Sadrita404/Low-Key/IMAGES/21.png

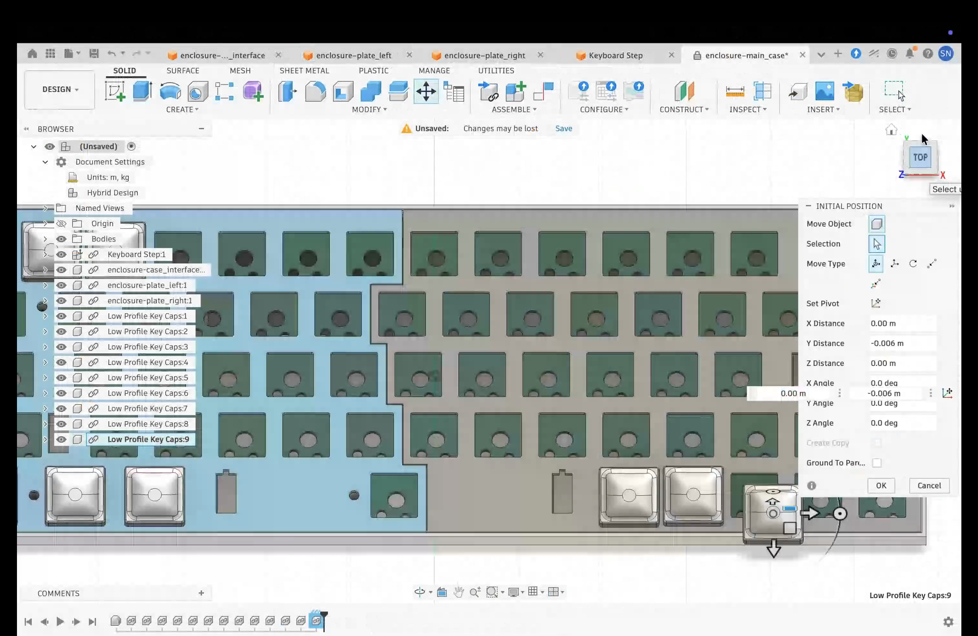
IMAGES/21.png
