Sadrita404/Low-Key/BILL/bill 1.png

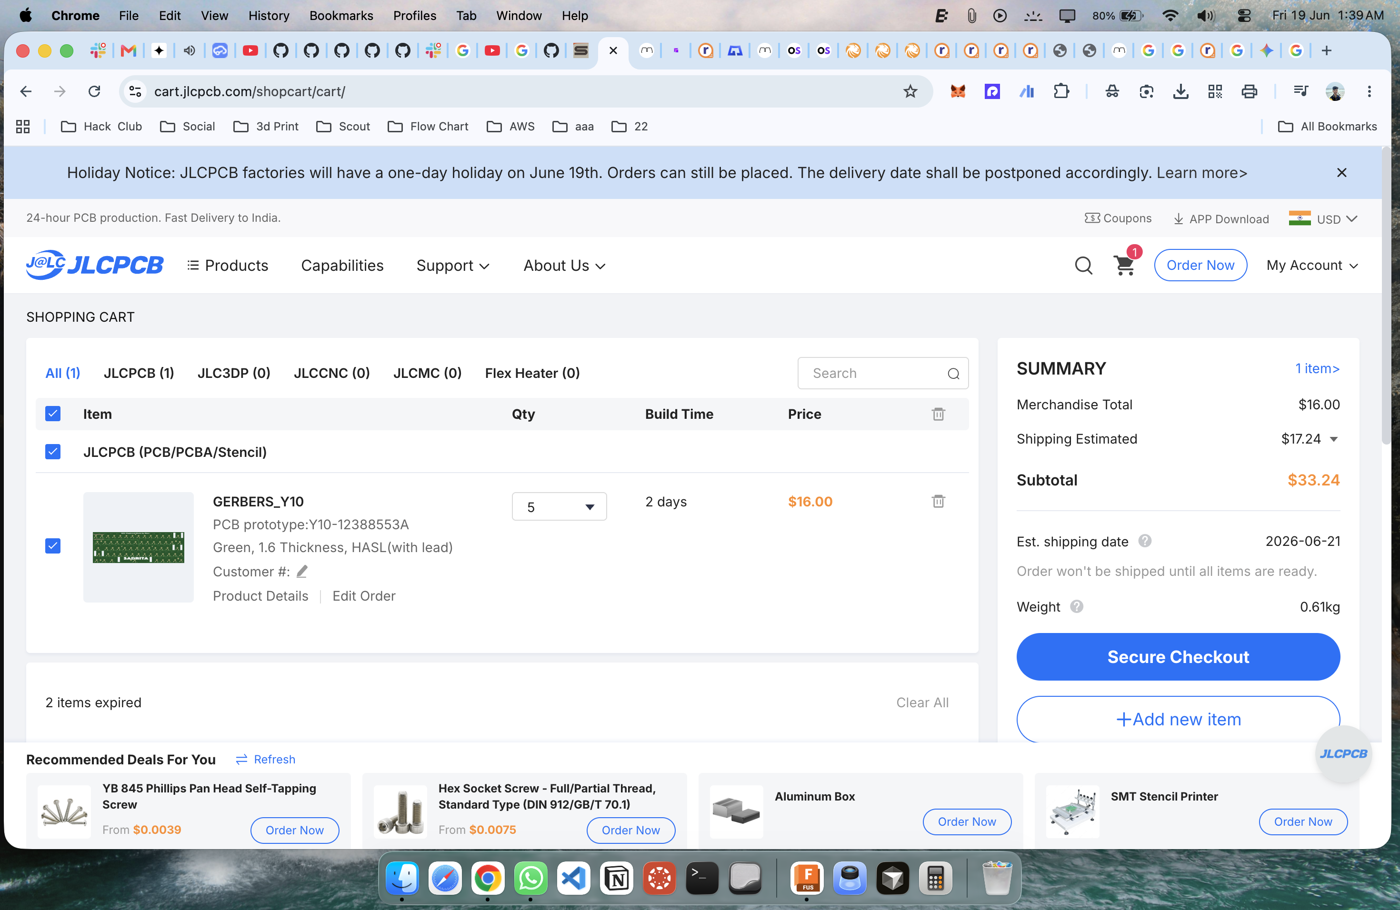
BILL/bill 1.png
