Sadrita404/Low-Key/BILL/bill 2.png

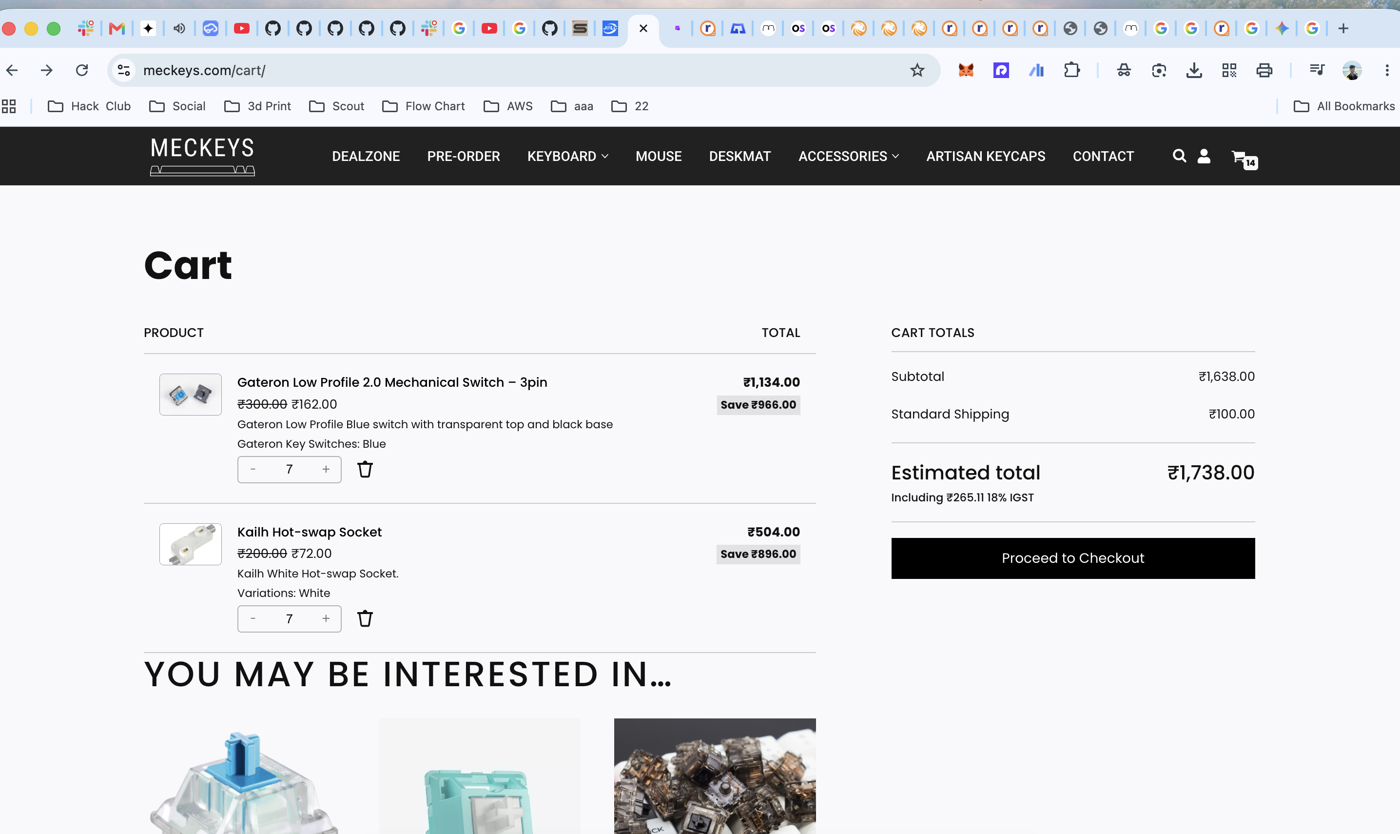
BILL/bill 2.png
