Sadrita404/Low-Key/BILL/bill 3.png

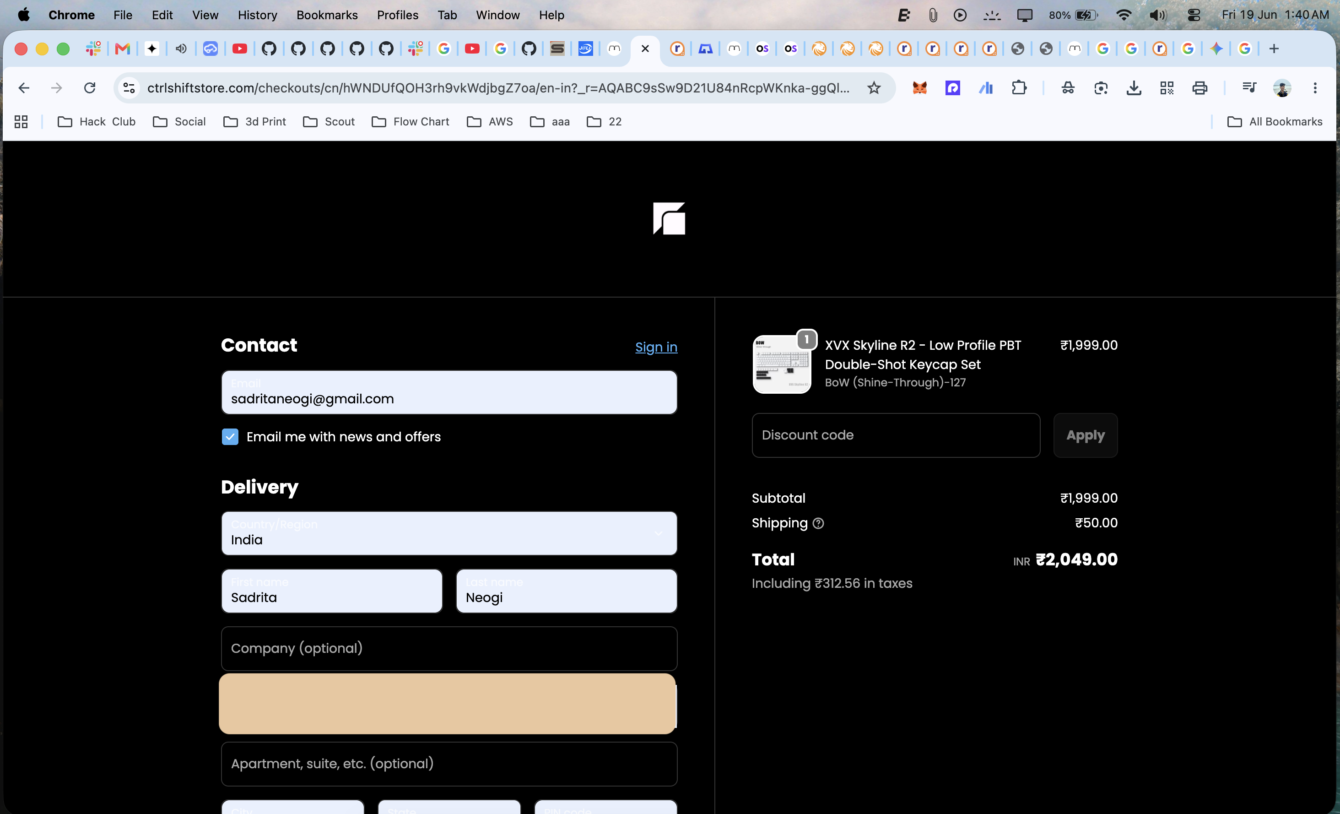
BILL/bill 3.png
