Sadrita404/Low-Key/BILL/bill 4.png

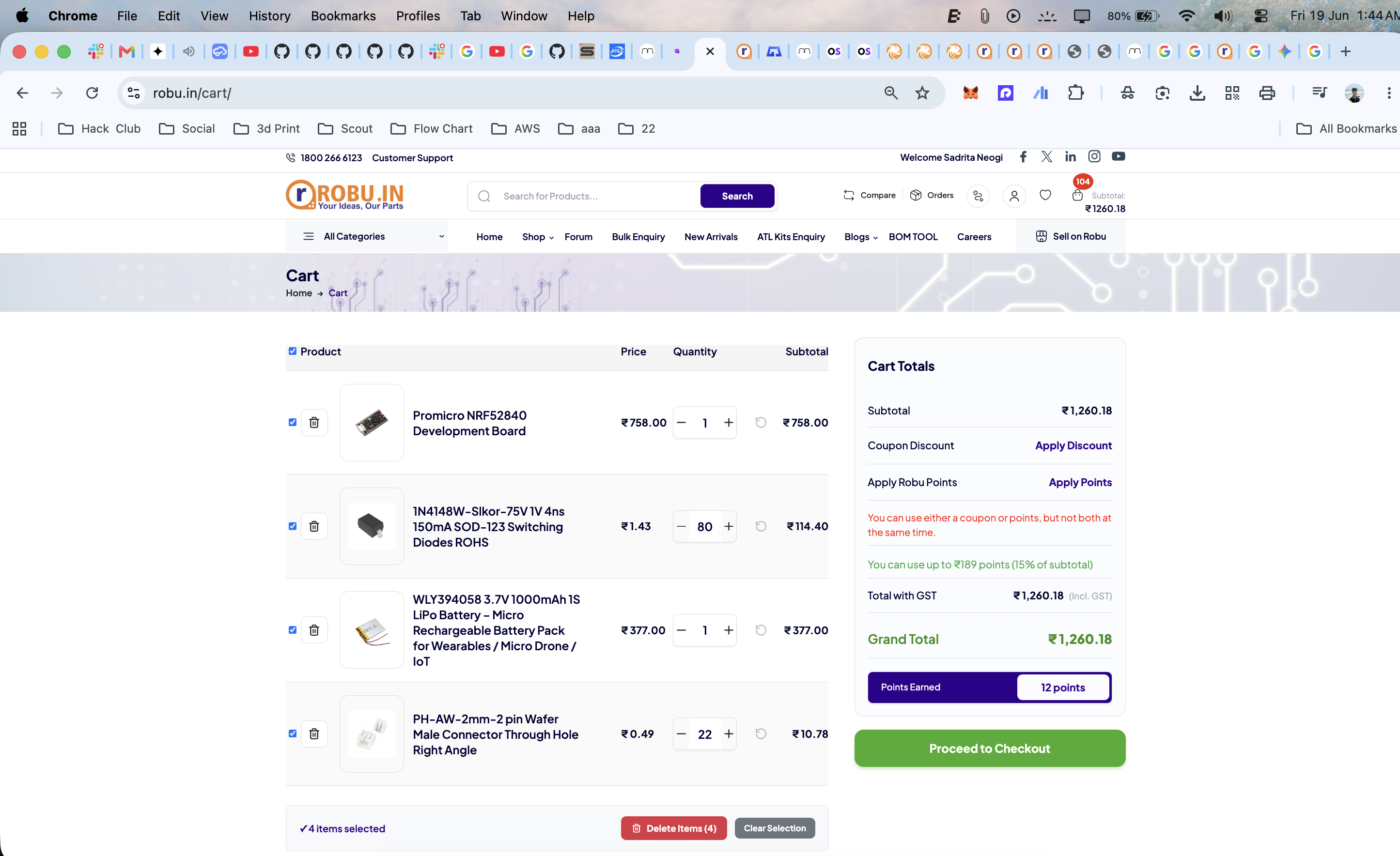
BILL/bill 4.png
