Sadrita404/Low-Key/BILL/bill 5.png

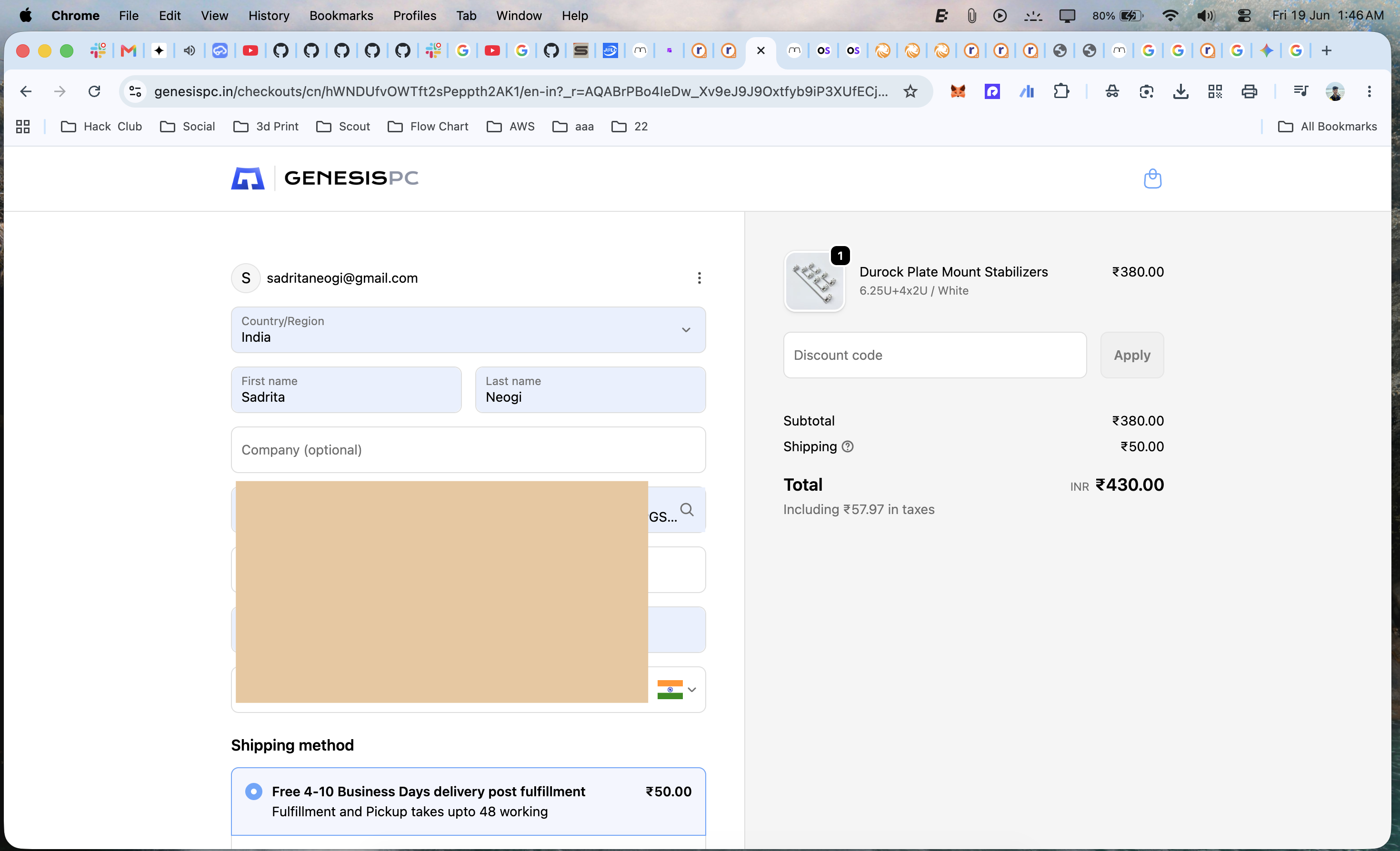
BILL/bill 5.png
