Sadrita404/Low-Key/BILL/bill 6.png

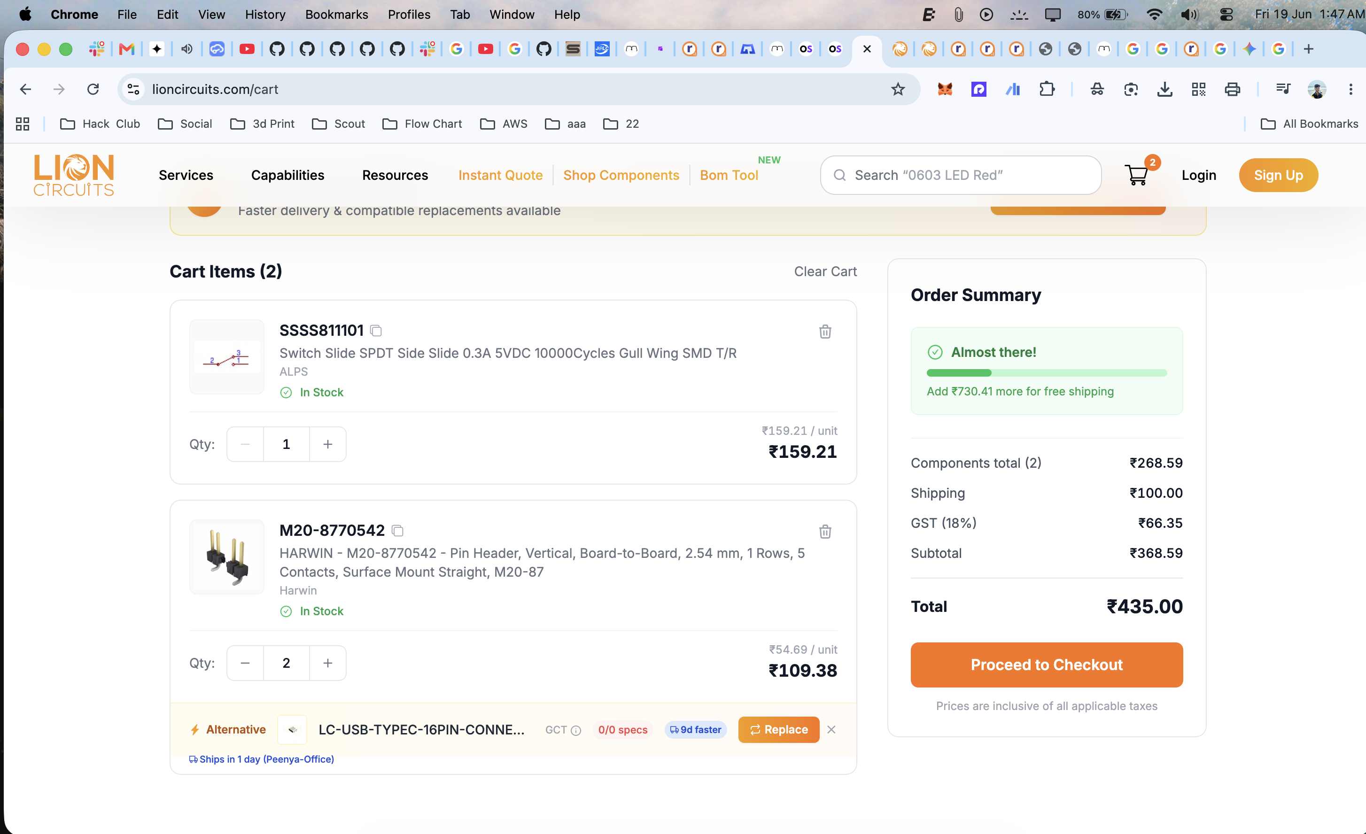
BILL/bill 6.png
