Sadrita404/Low-Key/IMAGES/3.png

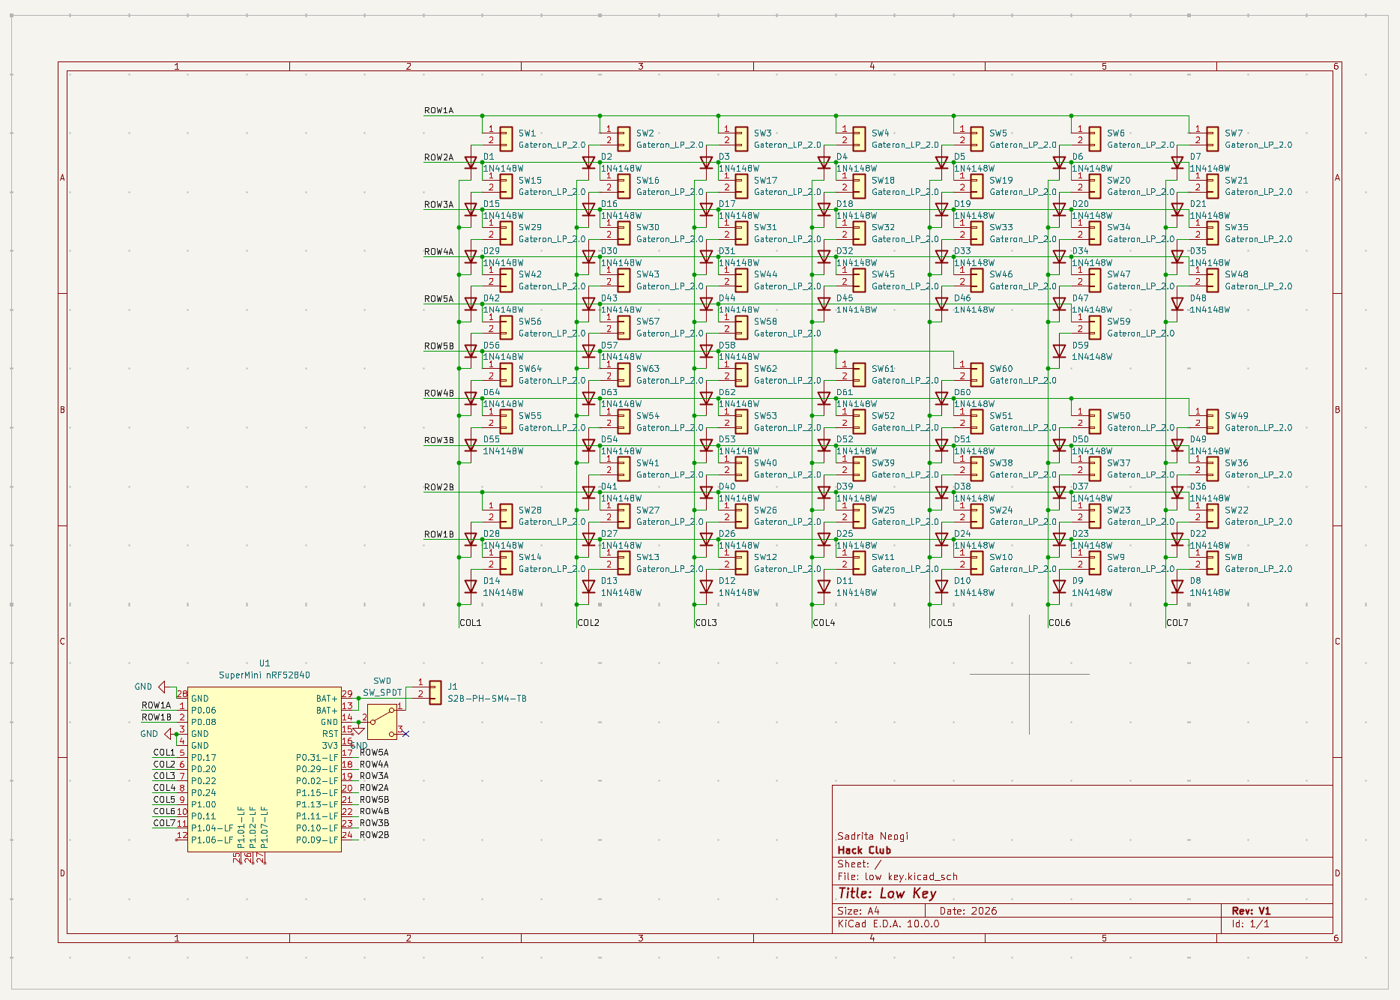
IMAGES/3.png
