Sadrita404/Low-Key/IMAGES/11.png

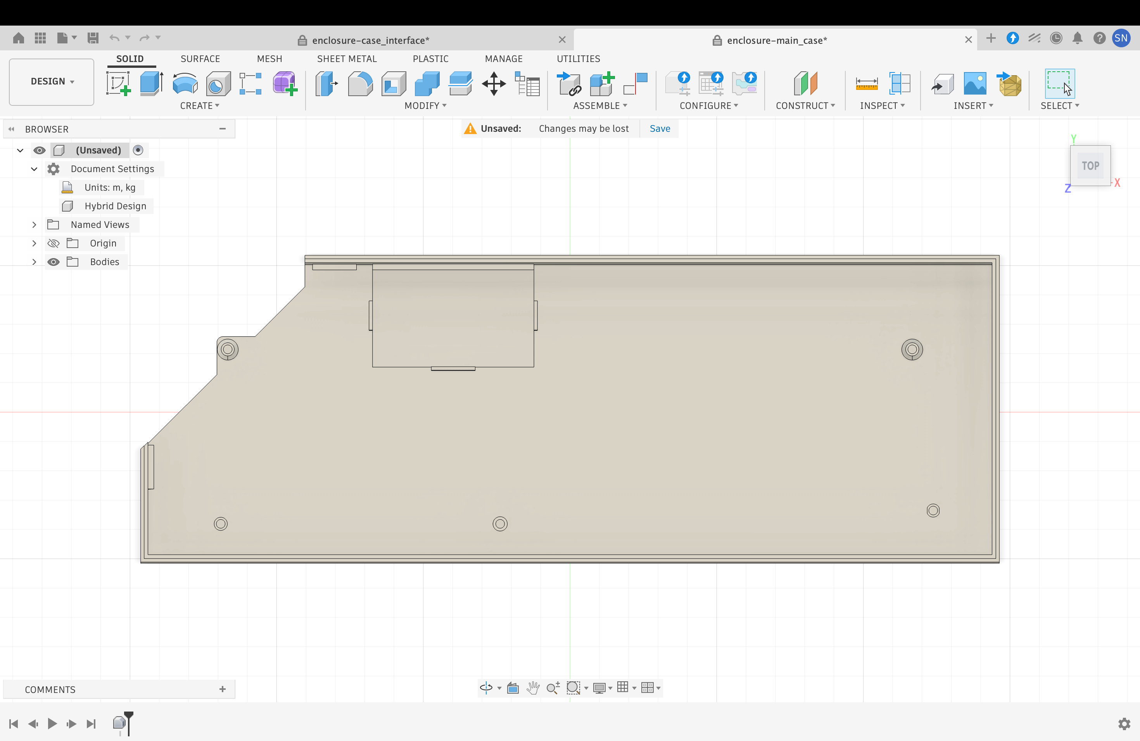
IMAGES/11.png
