Sadrita404/Low-Key/IMAGES/12.png

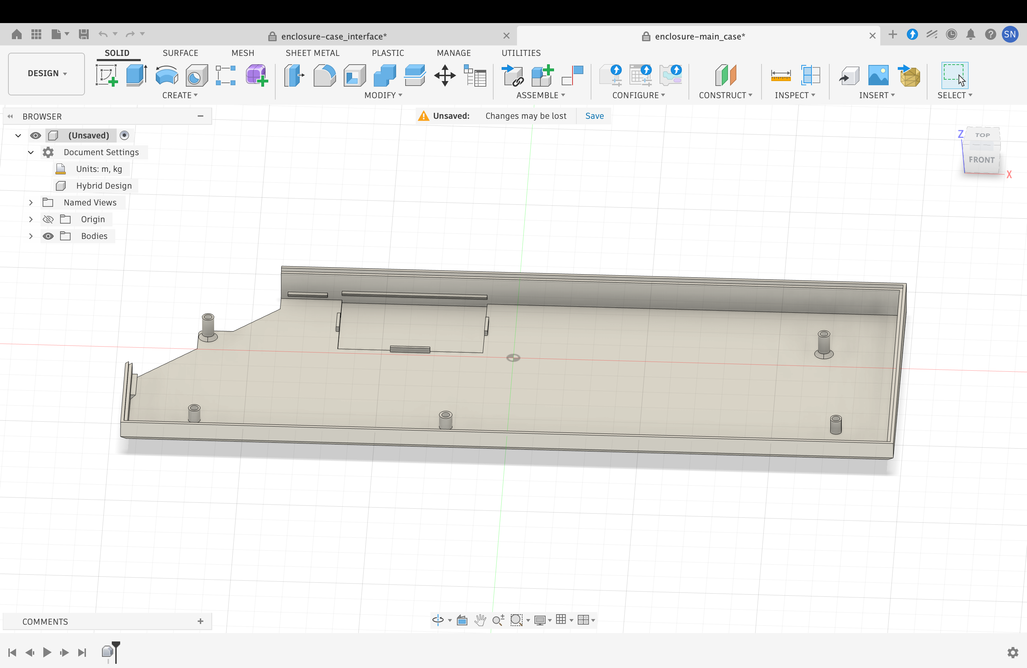
IMAGES/12.png
