Sadrita404/Low-Key/IMAGES/13.png

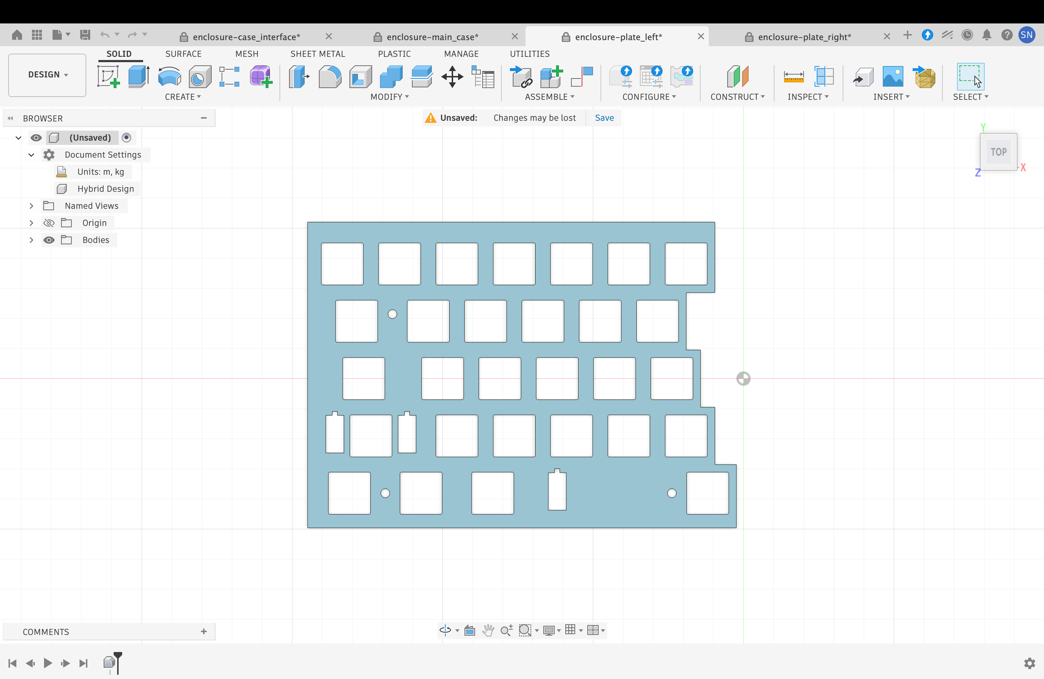
IMAGES/13.png
