Sadrita404/Low-Key/IMAGES/14.png

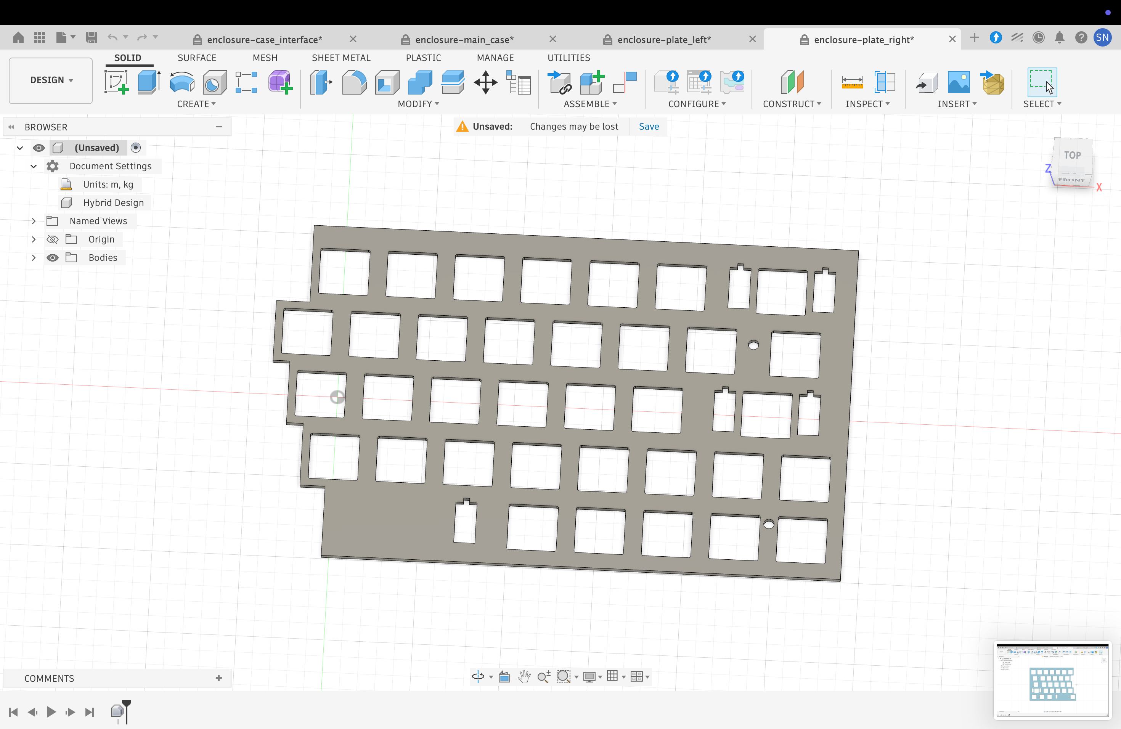
IMAGES/14.png
