Sadrita404/Low-Key/IMAGES/15.png

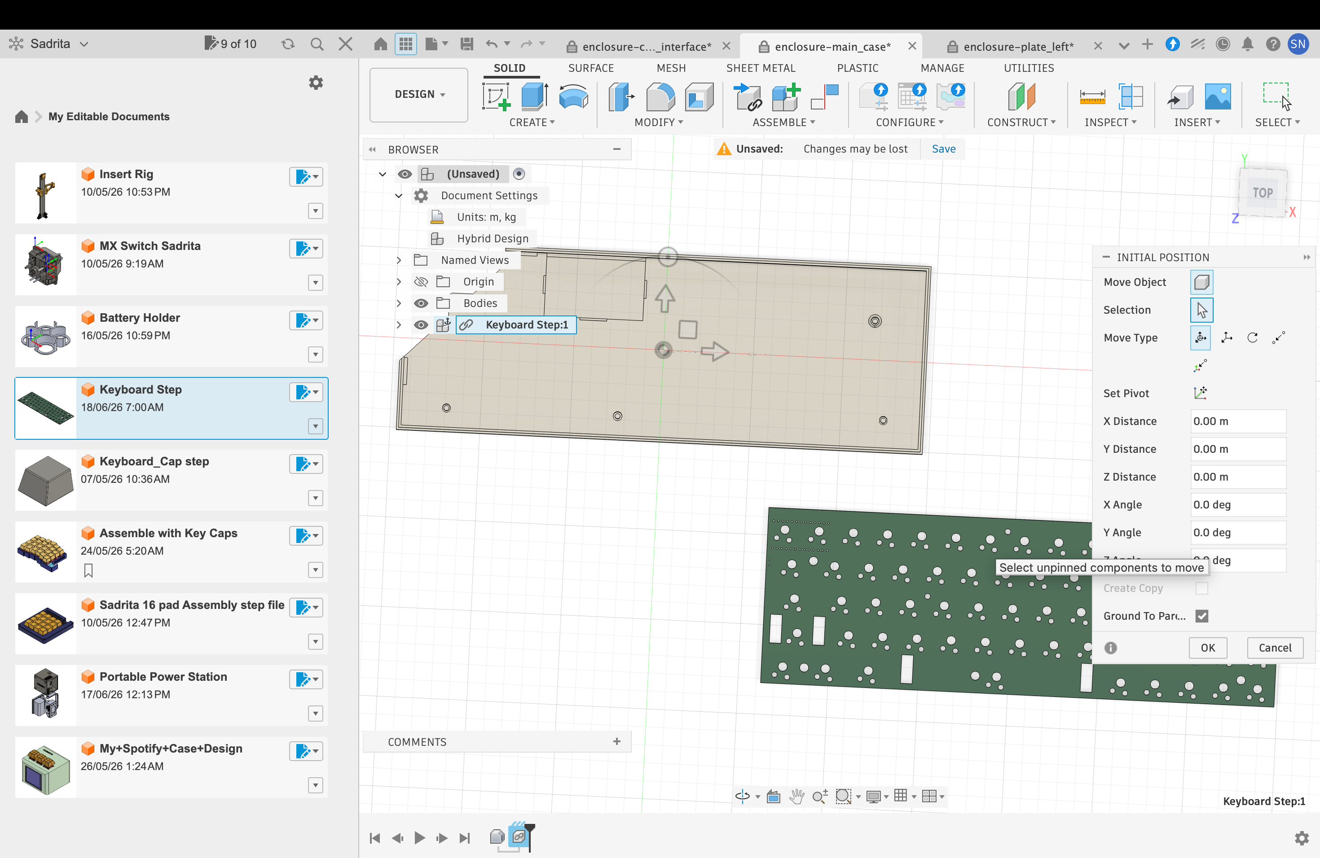
IMAGES/15.png
