Sadrita404/Low-Key/IMAGES/16.png

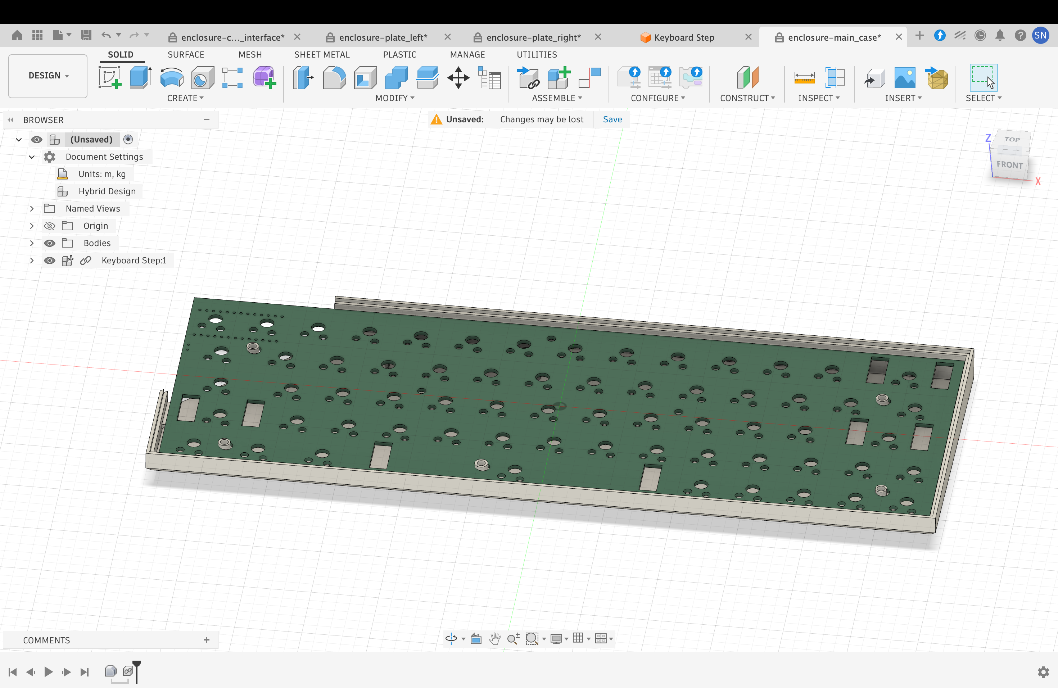
IMAGES/16.png
