Sadrita404/Low-Key/IMAGES/17.png

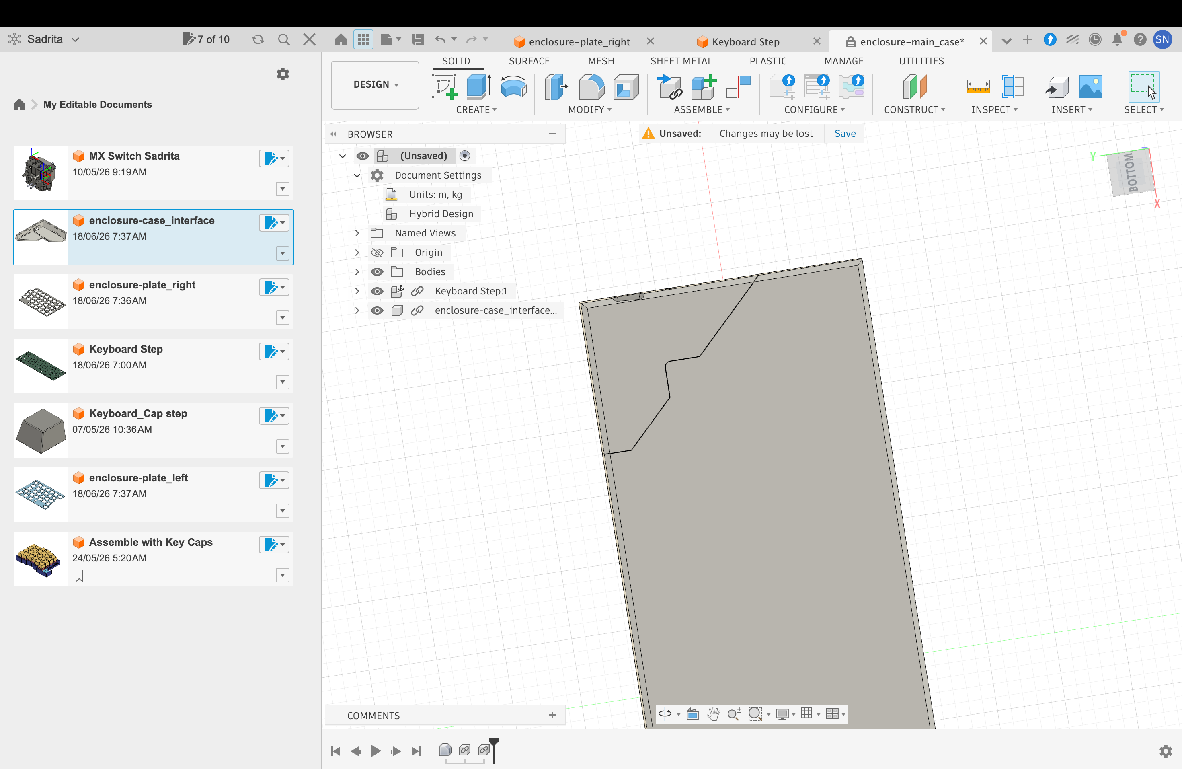
IMAGES/17.png
