Sadrita404/Low-Key/IMAGES/18.png

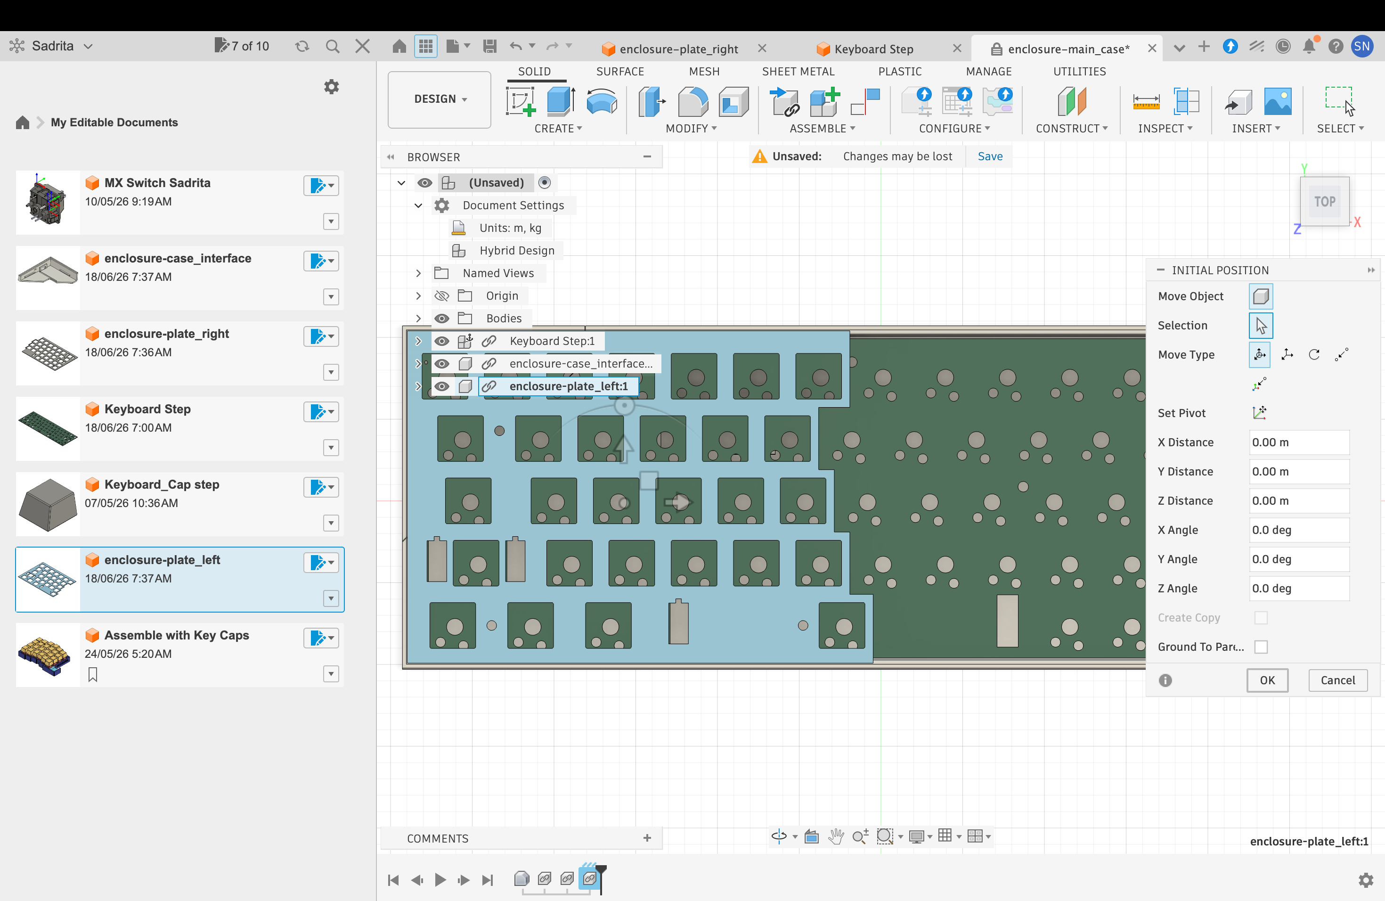
IMAGES/18.png
