Sadrita404/Low-Key/IMAGES/19.png

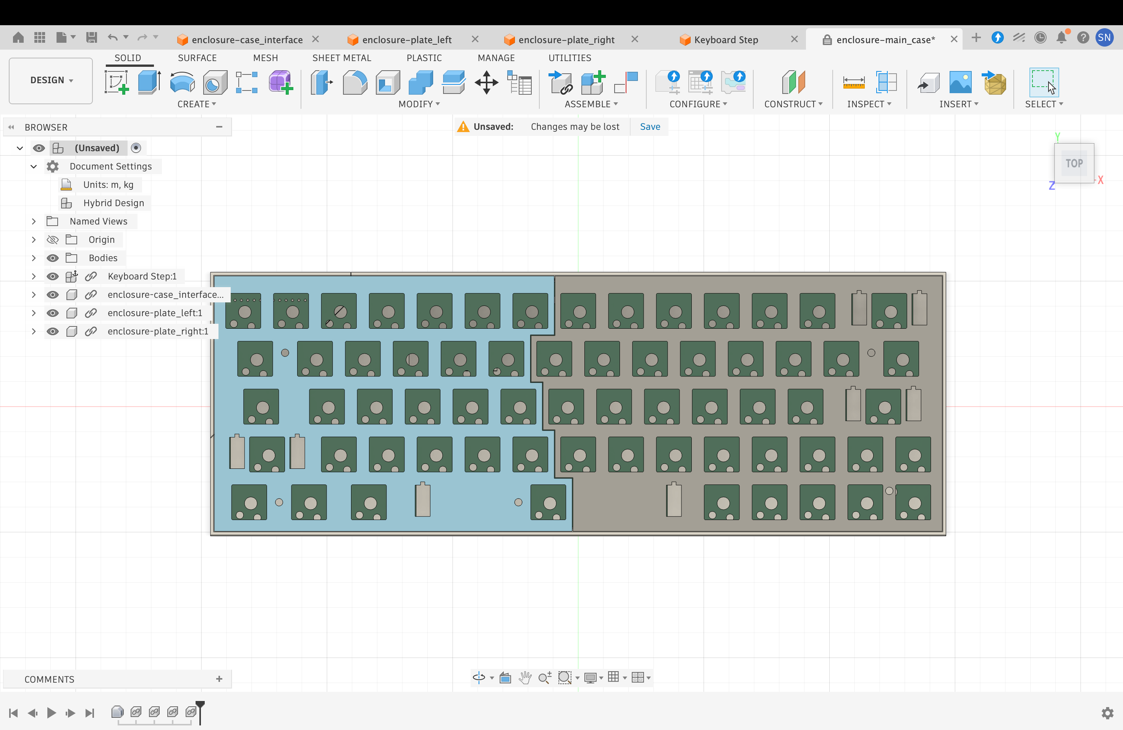
IMAGES/19.png
