Sadrita404/Low-Key/IMAGES/20.png

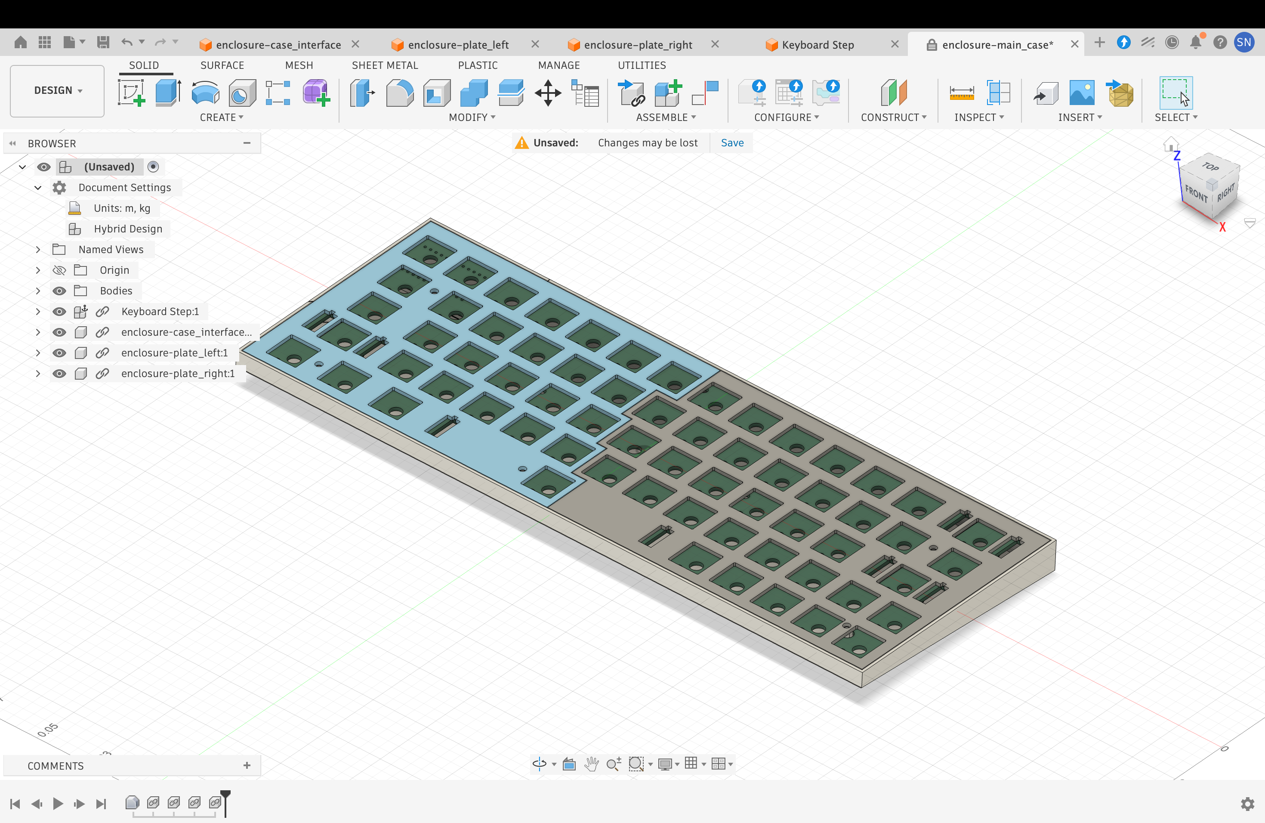
IMAGES/20.png
