Sadrita404/Low-Key/IMAGES/25.png

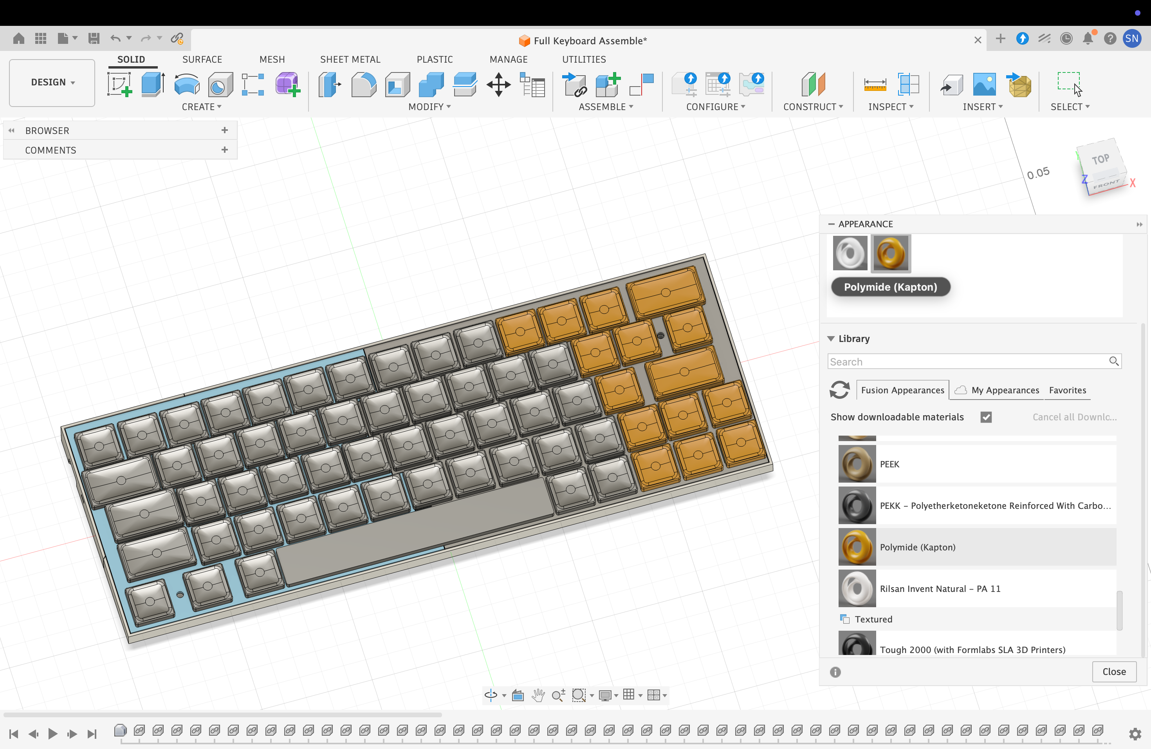
IMAGES/25.png
