Sadrita404/Low-Key/IMAGES/26.png

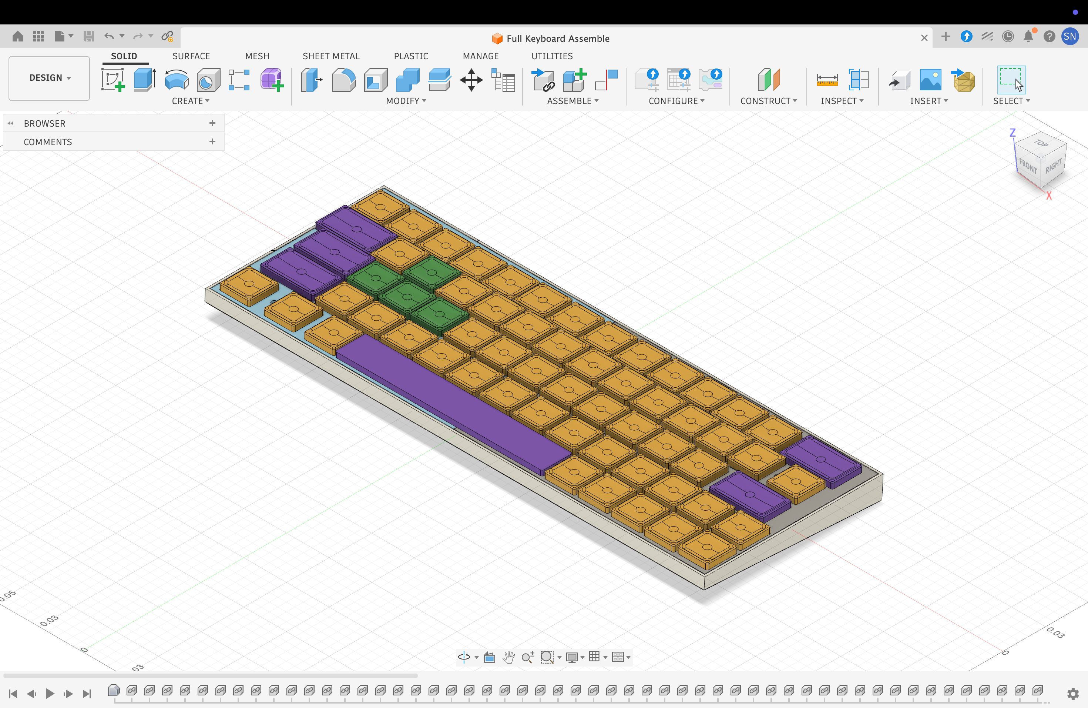
IMAGES/26.png
