Sadrita404/Low-Key/IMAGES/27.png

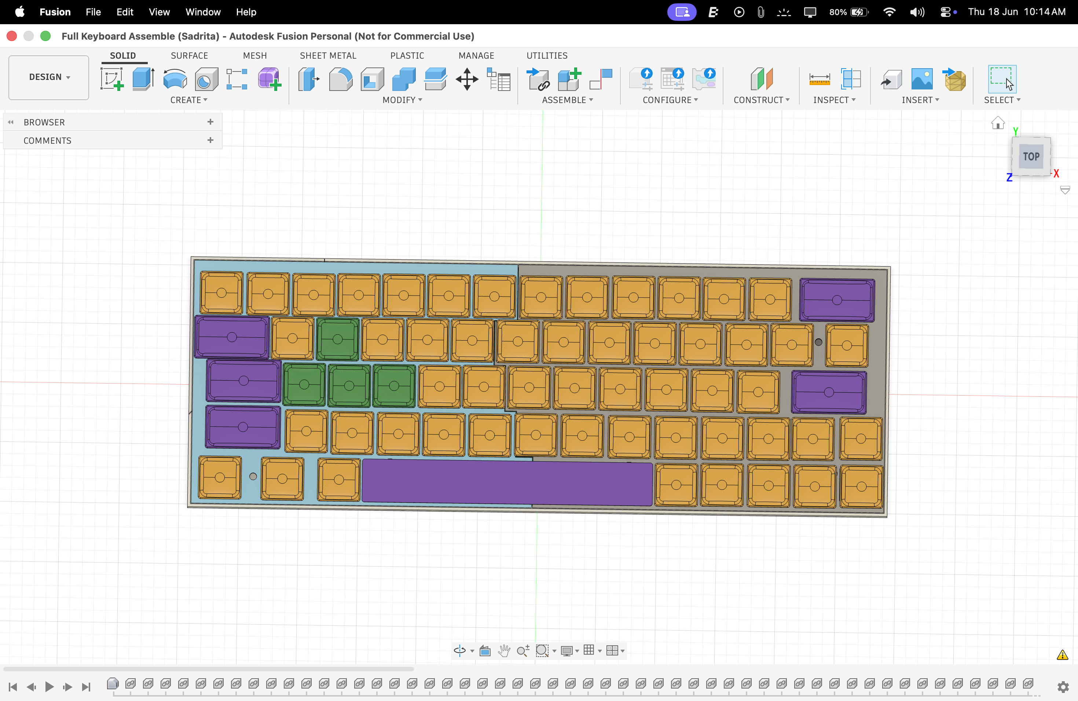
IMAGES/27.png
