Sadrita404/Low-Key/IMAGES/28.png

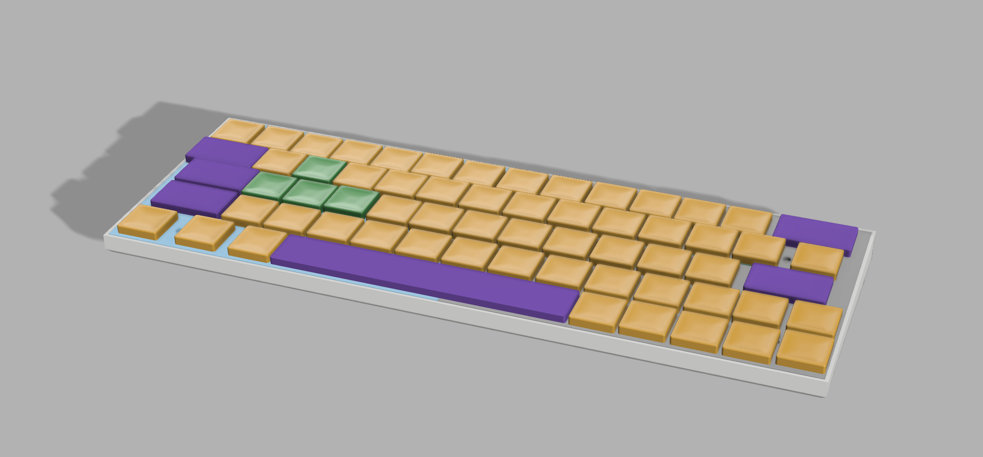
IMAGES/28.png
