Sadrita404/Low-Key/IMAGES/29.png

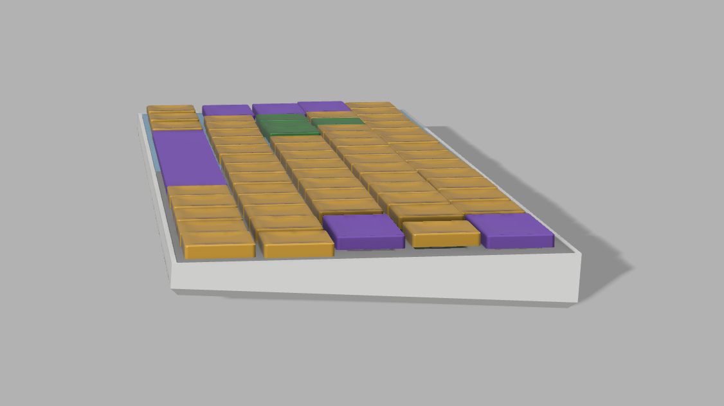
IMAGES/29.png
