Sadrita404/Low-Key/IMAGES/30.png

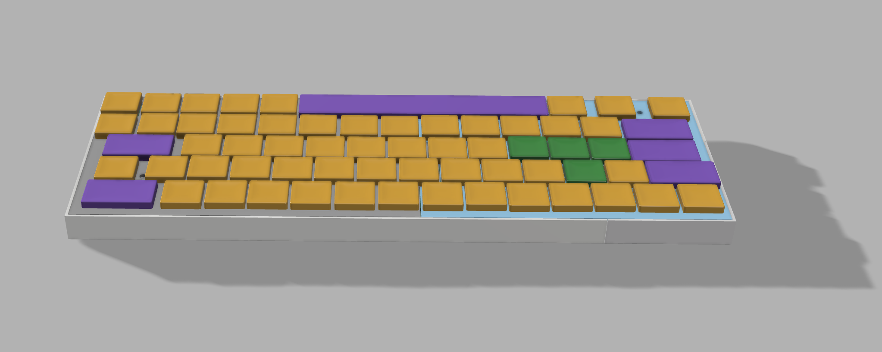
IMAGES/30.png
