Sadrita404/Low-Key/IMAGES/31.png

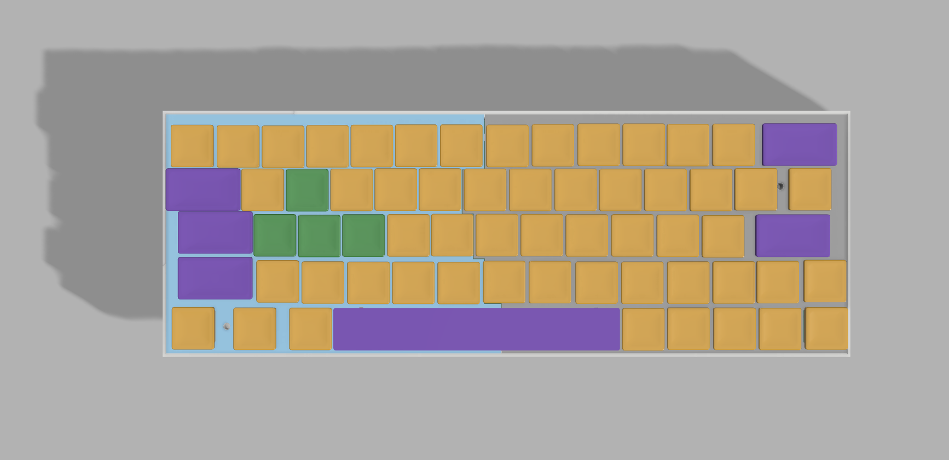
IMAGES/31.png
